k-nowicki/esp32_weather_logger/data/www/dcim/0/current.jpg

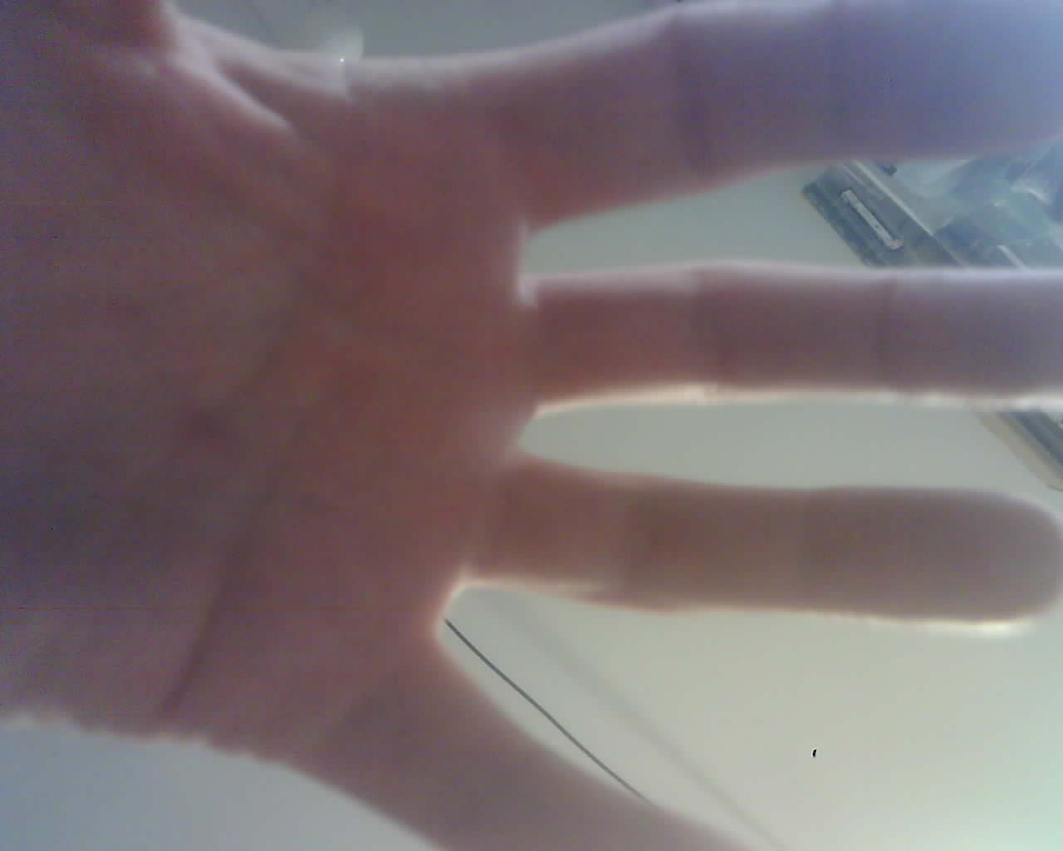
data/www/dcim/0/current.jpg
