k-nowicki/esp32_weather_logger/main/tasks/vSDAVGLGTask.cpp

/* KK Weather Station
 * SDAVGLG_TASK_PRIO Task
 *
 * Platform: ESP32 (Tested on ESP32-CAM Development Board)
 * See project documentation for more detailed description.
 *
 *  Copyright (c) <2022> <Karol Nowicki>
 *
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
 *  THE SOFTWARE IS PROVIDED "AS IS", WITHOUT WARRANTY OF ANY KIND, EXPRESS OR
 *  IMPLIED, INCLUDING BUT NOT LIMITED TO THE WARRANTIES OF MERCHANTABILITY,
 *  FITNESS FOR A PARTICULAR PURPOSE AND NONINFRINGEMENT. IN NO EVENT SHALL THE
 *  AUTHORS OR COPYRIGHT HOLDERS BE LIABLE FOR ANY CLAIM, DAMAGES OR OTHER
 *  LIABILITY, WHETHER IN AN ACTION OF CONTRACT, TORT OR OTHERWISE, ARISING FROM,
 *  OUT OF OR IN CONNECTION WITH THE SOFTWARE OR THE USE OR OTHER DEALINGS IN THE
 *  SOFTWARE.
*/

//System
#define _POSIX_SOURCE
#include <dirent.h>
#include <errno.h>
#include <stdio.h>
#undef _POSIX_SOURCE
#include <stdlib.h>
#include <string.h>
#include <sys/unistd.h>
#include <sys/stat.h>
#include "freertos/FreeRTOS.h"
#include "freertos/task.h"
#include "freertos/semphr.h"
#include "esp_system.h"
#include "esp_log.h"
#include "esp_err.h"
#include "esp_event.h"
#include "esp_attr.h"
#include "esp_sleep.h"
#include "esp_sntp.h"
#include <time.h>
#include "nvs_flash.h"
#include "esp_vfs_fat.h"
#include "sdmmc_cmd.h"
#include "driver/sdmmc_host.h"

//App headers
#include "tasks.h"

static void replace_or_continue_current_avglg_file(void);
static void rename_avglg_file(tm *);
static bool is_date_changed();
extern uint8_t begin_csvlg_file(const char *);
extern uint8_t end_csvlg_file(const char *);

static const char *TAG = "SDAVGLG";
#define CURR_AVGLG_FNAME static_cast<const char *>(SD_MOUNT_POINT AVG_LOG_FILE_DIR"/CURRENT.CSV")



/*******************************************************************************
 * @brief Task responsible for logging average measurements to CSV files on SD card.
 *
 * Handles log files
 * Once every LOGGING_INTERVAL_MS:
 *    - collect measurements for averaging
 * Once every AVG_MESUREMENTS_NO:
 *    - append new measurements to current avg log file (open file, append, close file)
 *    - ensures sd card works (this should and probably will be moved to another task)
 * Once every 24 hours (at 00:00:00)
 *    - end and rename current log file to yesterdays date
 *    - begin new log file
 *
 * @param arg
 *
 */
void vSDAVGLGTask(void*){
  TickType_t xLastWakeTime;
  time_t file_time_t;
  struct tm file_tm;
  measurement measurements, avg_measurements;
  measurement measurements_buf[AVG_MESUREMENTS_NO];
  static int m_cnt = 0;
  static unsigned long long avg_time = 0;
  FILE *f;

  //Wait until RTC sends notify that is synchronized with external RTC
  ulTaskNotifyTakeIndexed( AVG_LOGGER_NOTIFY_ARRAY_INDEX, pdTRUE, portMAX_DELAY );
  //for desynchronize RTCTask logs with this task logs to not interfere each other
  vTaskDelay(pdMS_TO_TICKS(200));

  xLastWakeTime = xTaskGetTickCount();   //https://www.freertos.org/xtaskdelayuntiltask-control.html
  //Log file must be todays log file
  //if older log file exists and hasn't been renamed should be ended and renamed now
  replace_or_continue_current_avglg_file();
  ESP_LOGI(TAG, "Start logging measurements to AVG CSV on SD card.");
  while (1) {

   /**
    * If date has changed than current log file is ended, renamed to yesterdays
    * date and new current log file is opened.
    */
    if( is_date_changed() ){
      ESP_LOGI(TAG, "New day, new log file. Renaming current log to yesterdays date.");
      end_csvlg_file(CURR_AVGLG_FNAME);
      //get time of yesterday:
      file_time_t = time(NULL) - (24 * 60 * 60);
      localtime_r(&file_time_t, &file_tm);
      //Rename original file
      rename_avglg_file(&file_tm);
      begin_csvlg_file(CURR_AVGLG_FNAME);
    }

   /**
    * Store new data entry to buffer once every execution
    */
    measurements_buf[m_cnt++] = get_latest_measurements();

    /**
     * If get AVG_MESUREMENTS_NO measurements, then average them and store
     */
    if(m_cnt >= AVG_MESUREMENTS_NO){
      for(int i = 0; i < m_cnt; i++){
        measurements.eTemp += measurements_buf[i].eTemp;
        measurements.humi += measurements_buf[i].humi;
        measurements.iTemp += measurements_buf[i].iTemp;
        measurements.lux += measurements_buf[i].lux;
        measurements.pres += measurements_buf[i].pres;
        measurements.wind += measurements_buf[i].wind;
        avg_time += measurements_buf[i].time;
      }
      //average all values by number measurements_count
      measurements.eTemp /= m_cnt;
      measurements.humi /= m_cnt;
      measurements.iTemp /= m_cnt;
      measurements.lux /= m_cnt;
      measurements.pres /= m_cnt;
      measurements.wind /= m_cnt;
      measurements.time = avg_time/m_cnt;

      /**
       * Store new line in CURR_AVGLG_FNAME
       */
      f = fopen(CURR_AVGLG_FNAME, "a+");
      if (f == NULL) {  //if can not open file
        fclose(f);
        ESP_LOGE(TAG, "Failed to open log file!");
        ensure_card_works();
      }else{
        //Prepare and store log entry
        fprintf(f, "%lld,%3.2F,%3.2F,%d,%5.2F,%4.2f,%3.3f\n",
                      static_cast<long long>(measurements.time),
                      measurements.iTemp,
                      measurements.eTemp,
                      static_cast<int>(measurements.humi),
                      measurements.lux,
                      measurements.pres,
                      measurements.wind);
        fclose(f);
        // reset helper variables
        m_cnt = 0; avg_time = 0;
        measurements.eTemp = 0;
        measurements.humi = 0;
        measurements.iTemp = 0;
        measurements.lux = 0;
        measurements.pres = 0;
        measurements.wind = 0;
        measurements.time = 0;
      }
    }
    // Wait for the next cycle exactly 1 second- it is critical to .
    xTaskDelayUntil( &xLastWakeTime, pdMS_TO_TICKS(LOGGING_INTERVAL_MS) );
  }
}


/**
 * Check if CURR_LOG_FNAME exists, begin file if not
 * If exists:
 *  - check last modification date,
 *  - if it is not today:
 *    - end that file with date from last modification
 *    - begin new log file
 *  - otherwise continue with that file
 */
void replace_or_continue_current_avglg_file(){
  time_t now =0, file_time_t =0;
  struct tm timeinfo, file_tm;
  struct stat fileStat;

  if(stat(CURR_AVGLG_FNAME, &fileStat) == ESP_OK){   //if file exists
    file_time_t = fileStat.st_mtime;      //get last modification time of the file
    now= time(NULL);                      //get now time
    localtime_r(&now, &timeinfo);         //modify both to localtime
    localtime_r(&file_time_t, &file_tm);
    ESP_LOGI(TAG, "CURRENT.CSV file last modification date: %4d-%2d-%2d", (file_tm.tm_year+1900), file_tm.tm_mon+1, file_tm.tm_mday);
    //if file mod yday older than now yday or file mod year older than now year
    if((file_tm.tm_year < timeinfo.tm_year) || (file_tm.tm_yday < timeinfo.tm_yday)){
      end_csvlg_file(CURR_AVGLG_FNAME);   //end that file
      rename_avglg_file(&file_tm);       //rename it with date of last modification.
      begin_csvlg_file(CURR_AVGLG_FNAME); //and begin new log file
    }
    return;
  }else{  //if file don't exist
    if(begin_csvlg_file(CURR_AVGLG_FNAME)){
      ESP_LOGE(TAG, "Can't create file: %s", CURR_AVGLG_FNAME);
    }
  }
}

/**
 * Change name of current log file to YYMMDD.LOG ex: 091222.LOG
 * @param time Pointer to tm struct with time that will be stored in filename
 *
 */
void rename_avglg_file(tm * time){
  char arch_log_filename[39];
  uint8_t status = 0;
  sprintf(arch_log_filename, "%s/%02d%02d%02d.CSV", SD_MOUNT_POINT AVG_LOG_FILE_DIR, time->tm_mday, time->tm_mon+1, static_cast<uint8_t>(time->tm_year-100)  );
  ESP_LOGI(TAG, "Renaming file %s to %s", CURR_AVGLG_FNAME, arch_log_filename);
  status = rename(CURR_AVGLG_FNAME, arch_log_filename);
  if (status != 0) {
    /*
     * TODO: Resolve problem with renaming
     * If reason is that file already exist, it should open that file, append data from current log, than close and rename
     * If reason is different than it should be reported to end user
     */
    ESP_LOGE(TAG, "Log file rename failed with error: %d", status);

  }
}


/**
 * Check if date is different than in previous call
 * @return true if date has changed, false otherwise.
 */
static bool is_date_changed(){
  time_t now;
  struct tm timeinfo;
  static int yday = -1;

  time(&now);  localtime_r(&now, &timeinfo);
  //at first call initialize yday as today
  if(yday == -1)
    yday = timeinfo.tm_yday;
  //check if date has changed
  if(yday != timeinfo.tm_yday){
    yday = timeinfo.tm_yday;
    return true;
  }
  else
    return false;
}
